michaelkroll/BLE-Shield/iphone/BLE-Shield/BLE-Shield/ble-shield.png

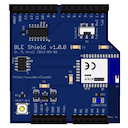
iphone/BLE-Shield/BLE-Shield/ble-shield.png
